Viper-7/CharlieBoy/src/joystick.cpp

/*
    Arduino Tetris
    Copyright (C) 2015 João André Esteves Vilaça 
    
    https://github.com/vilaca/Handheld-Color-Console

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
    You should have received a copy of the GNU General Public License along
    with this program; if not, write to the Free Software Foundation, Inc.,
    51 Franklin Street, Fifth Floor, Boston, MA 02110-1301 USA.
*/

#ifndef JOYSTICKCPP
#define JOYSTICKCPP

#include <Arduino.h>

// analog pins

#define XPIN        A6
#define YPIN        A7

// digital pin

#define FIREPIN     A5

// joystick center for both axis

#define CENTER      512

class Joystick
{
  public:

    // joystick position constants 
    
    static const int NEUTRAL = 0;
    static const int SOFT = 1;
    static const int HARD = 2;
    static const int HARDER = 3;

    static void init ()
    {
      pinMode ( FIREPIN, INPUT_PULLUP );
    }

    static int getX()
    {
      return getPosition(XPIN) * -1;
    }

    static int getY()
    {
      return getPosition(YPIN);// * -1;
    }

    static boolean fire()
    {
      return digitalRead(FIREPIN) == LOW;
    }

    static void waitForRelease()
    {
      while (fire());
    }

    static void waitForRelease(int howLong)
    {
      int c = 0;
      do
      {
        delay (10);
        c += 10;
      }
      while ((fire() || getY() != 0 || getX() != 0) && c < howLong);
    }

    static void waitForClick()
    {
      while (!fire());
    }

  private:

    static int getPosition (int pin)
    {
      const int n = analogRead(pin) - CENTER;

      return n / 128;
    }
};

#endif
